DavidNorthup/cube-solving-robot/application/samples/sample0.jpg

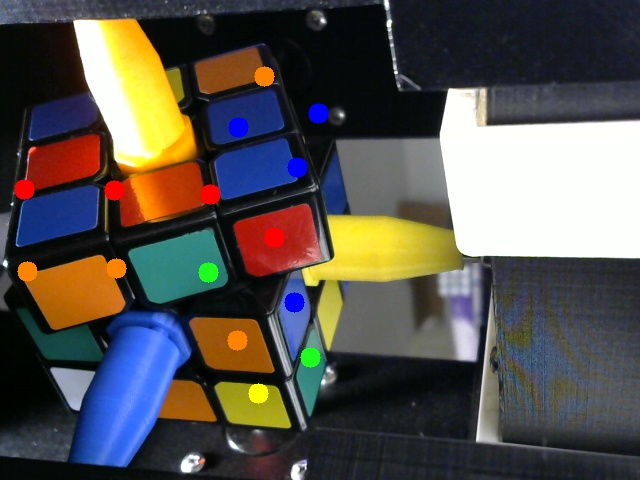
application/samples/sample0.jpg
